PRouzeau/Bowden-extruder-direct-drive/STL/Dirext_30_Tensioner.stl

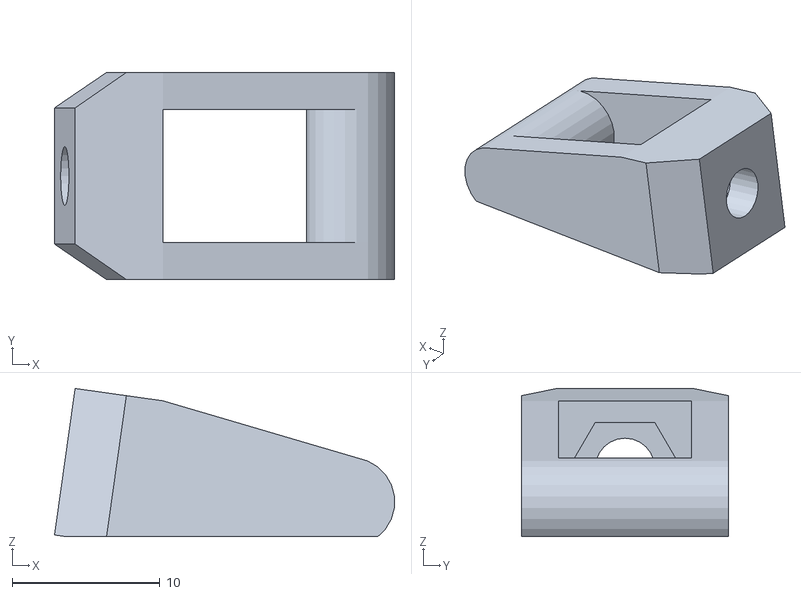
[picture p19: CAD file, 2016-03-28]
STL/Dirext_30_Tensioner.stl
23.0 x 14.0 x 10.0
