PRouzeau/Bowden-extruder-direct-drive/STL/Dirext_32_Thumbwheel.stl

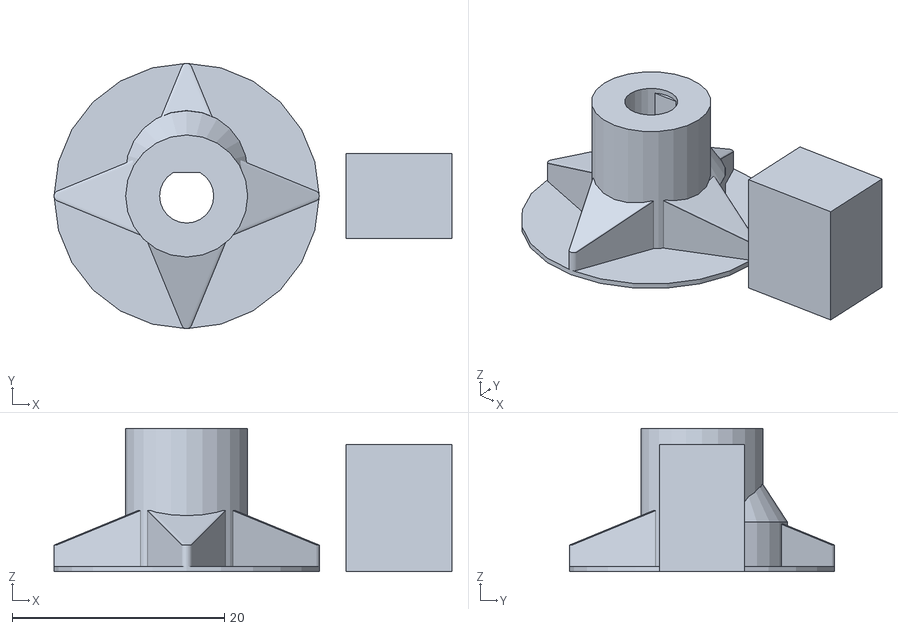
[picture p20: CAD file, 2016-03-28]
STL/Dirext_32_Thumbwheel.stl
37.5 x 25.0 x 13.5
