PRouzeau/Bowden-extruder-direct-drive/STL/Dirext_03_Dbl_extr_base_mirrored.stl

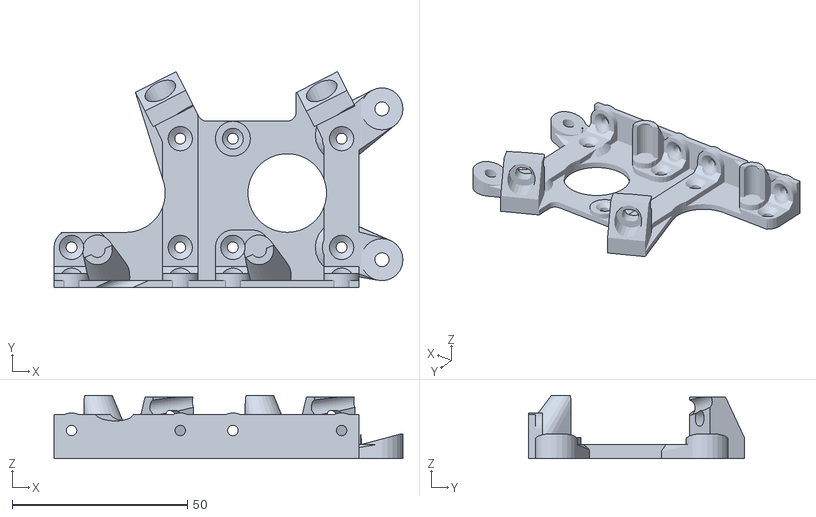
[picture p21: CAD file, 2016-03-28]
STL/Dirext_03_Dbl_extr_base_mirrored.stl
99.5 x 61.5 x 18.0
