PRouzeau/Bowden-extruder-direct-drive/STL/Dirext_12_Simple_extr_filguide.stl

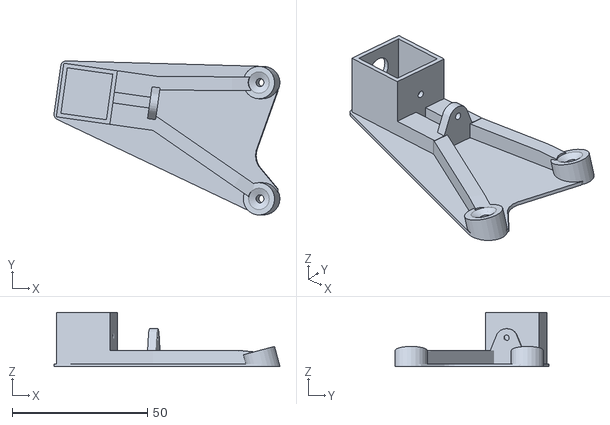
[picture p22: CAD file, 2016-03-28]
STL/Dirext_12_Simple_extr_filguide.stl
83.6 x 57.0 x 20.0
