PRouzeau/Bowden-extruder-direct-drive/Photos/Extruder_tensioner_install_P1040869.jpg

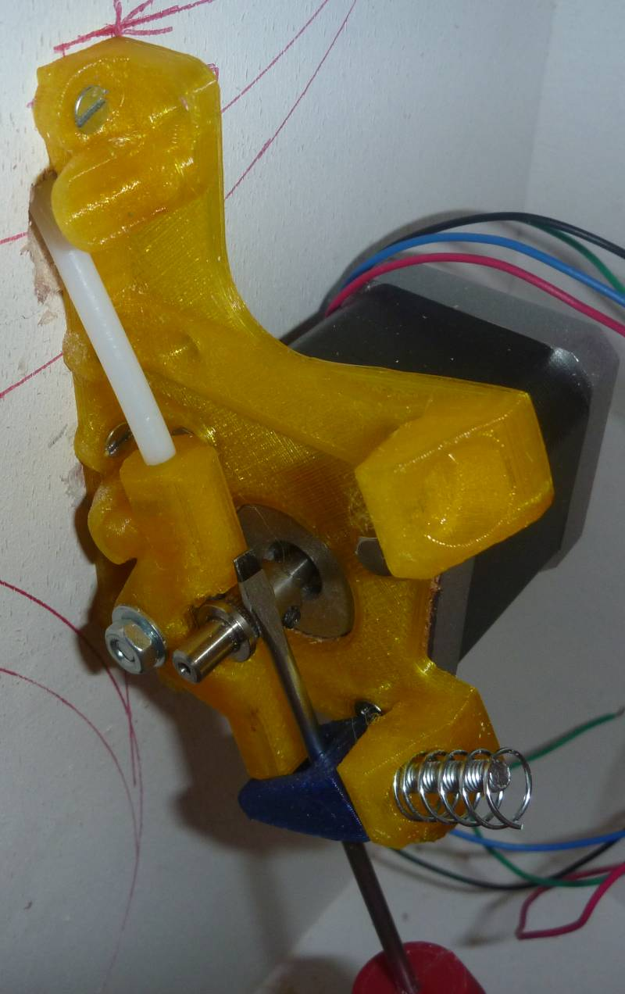
Photos/Extruder_tensioner_install_P1040869.jpg
