PRouzeau/Bowden-extruder-direct-drive/Photos/Extruder_wire_guide.jpg

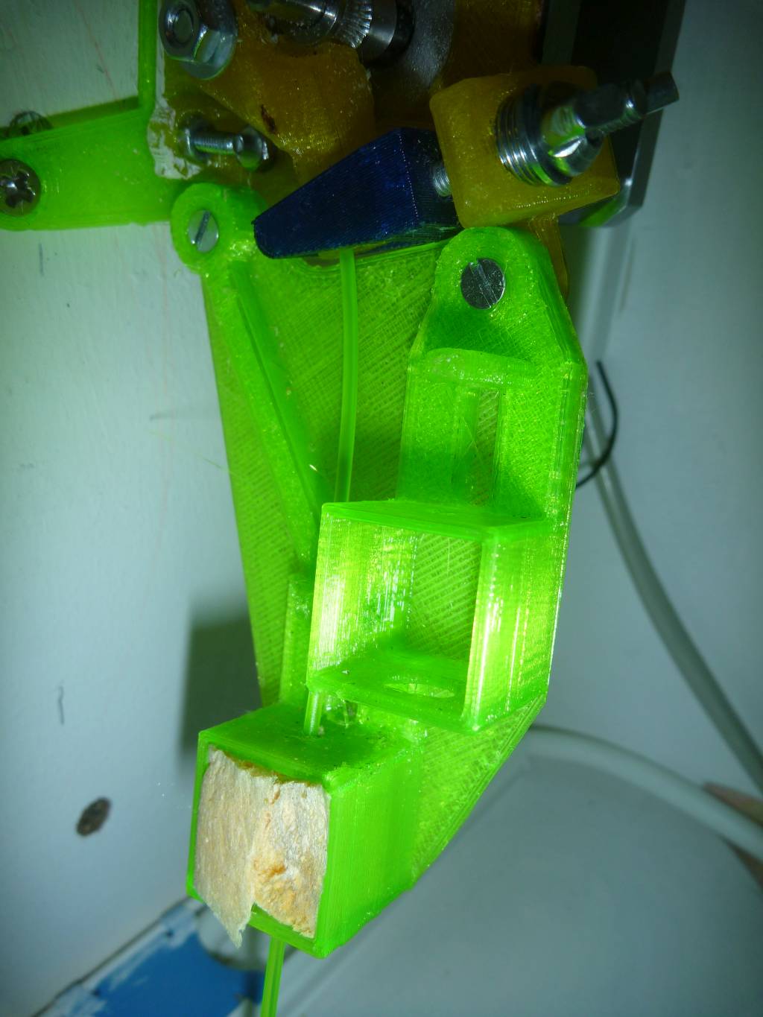
Photos/Extruder_wire_guide.jpg
